adoble/modular-audio/docs/img/controller-mcu.png

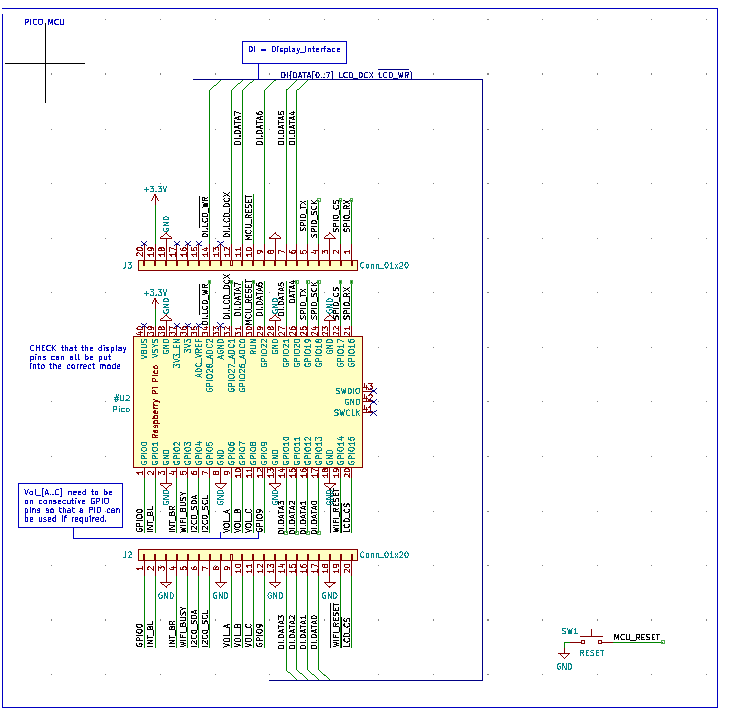
docs/img/controller-mcu.png
